CRM-UAM/Vector9000/competiciones/robolid2016/2016-04-08 11.16.23.jpg

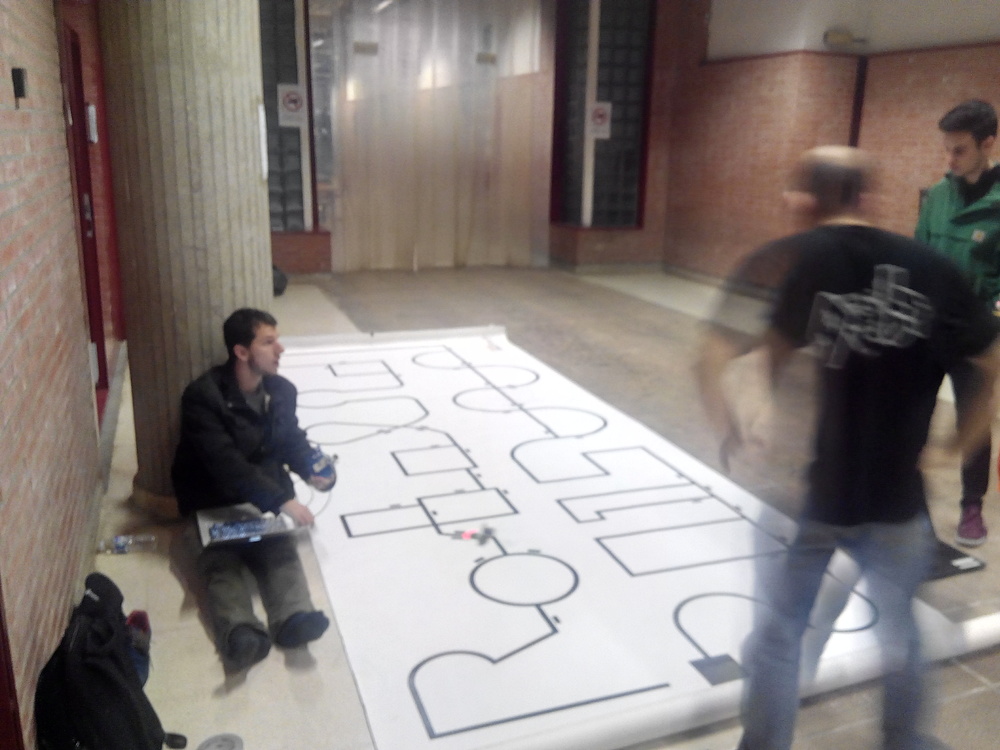
competiciones/robolid2016/2016-04-08 11.16.23.jpg
