CRM-UAM/Vector9000/img/2016-03-30 20.01.13.jpg

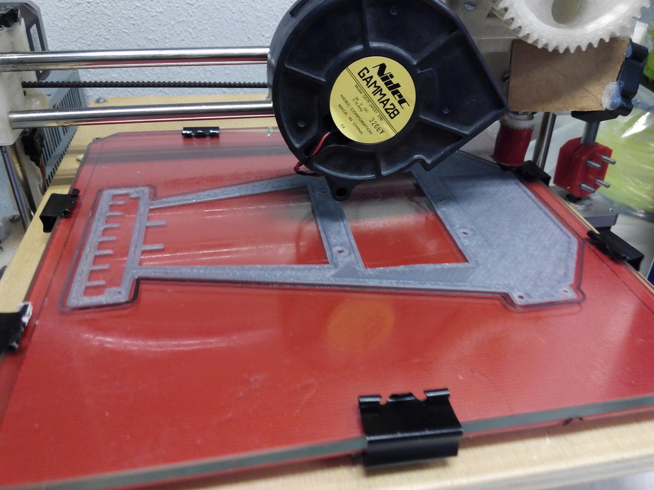
img/2016-03-30 20.01.13.jpg
