CRM-UAM/Vector9000/img/2016-04-03 20.19.17.jpg

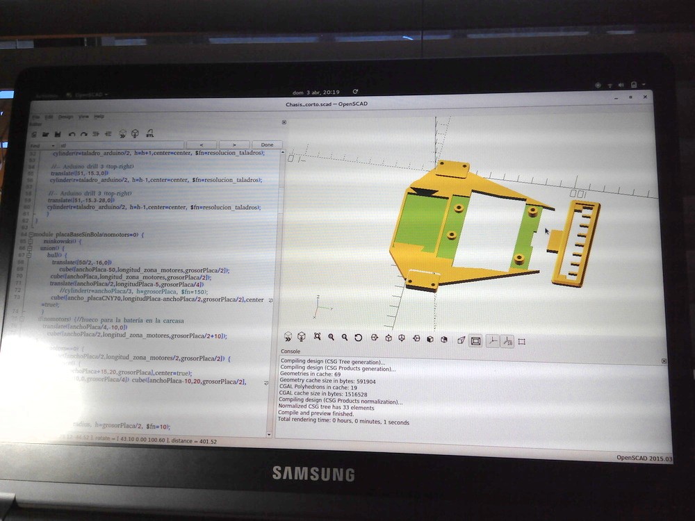
img/2016-04-03 20.19.17.jpg
