CRM-UAM/Vector9000/img/2016-04-04 11.50.08.jpg

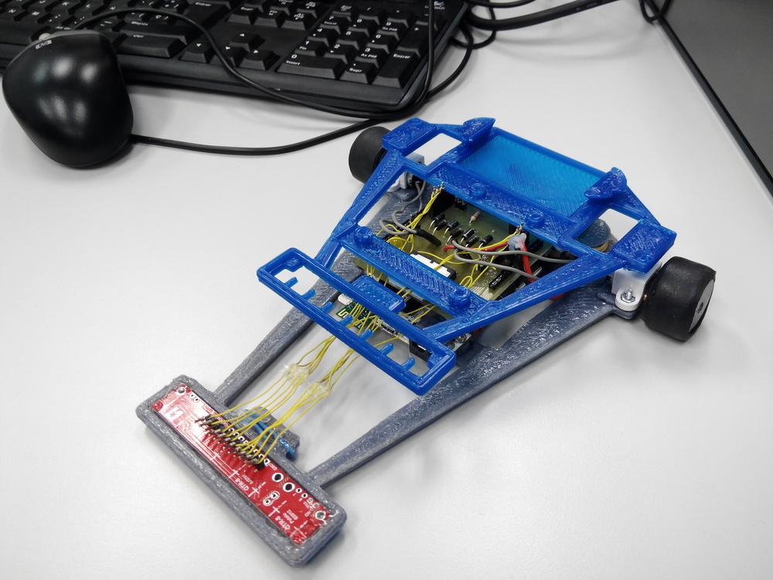
img/2016-04-04 11.50.08.jpg
