CRM-UAM/Vector9000/img/2016-04-08 11.37.30.jpg

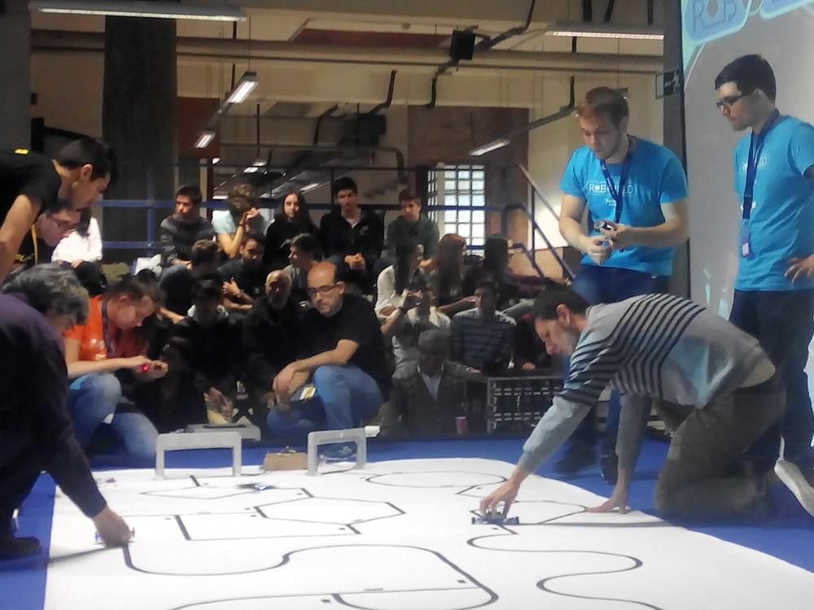
img/2016-04-08 11.37.30.jpg
