CRM-UAM/Vector9000/img/IMG-20160406-WA0005.jpg

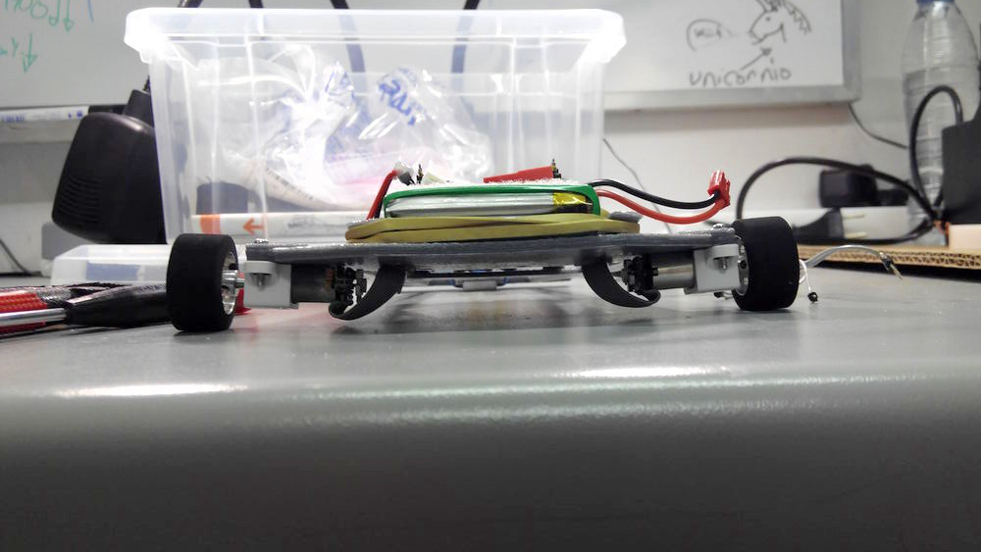
img/IMG-20160406-WA0005.jpg
