CRM-UAM/Vector9000/img/IMG-20160407-WA0009.jpg

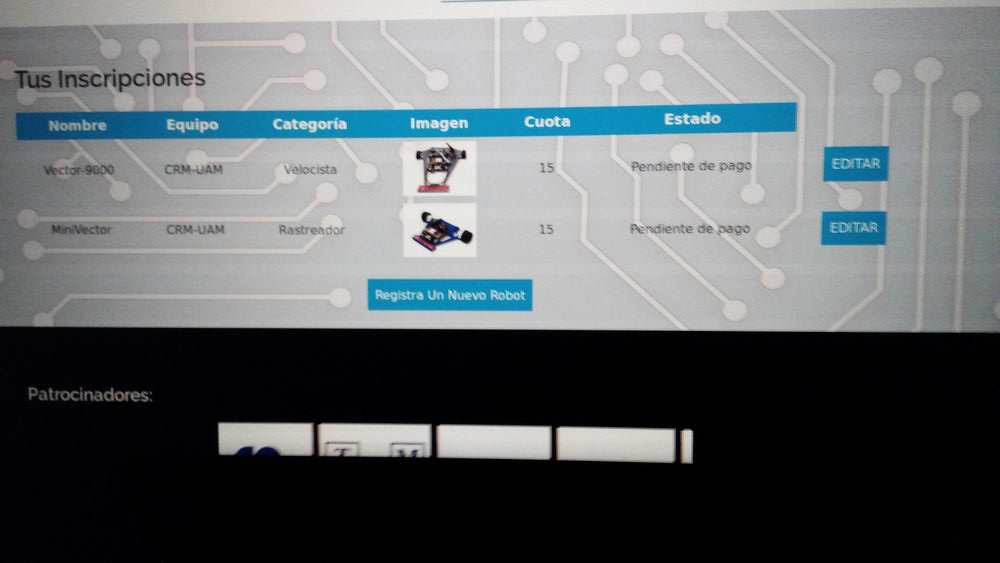
img/IMG-20160407-WA0009.jpg
