CRM-UAM/Vector9000/img/robots_robolid2016.jpg

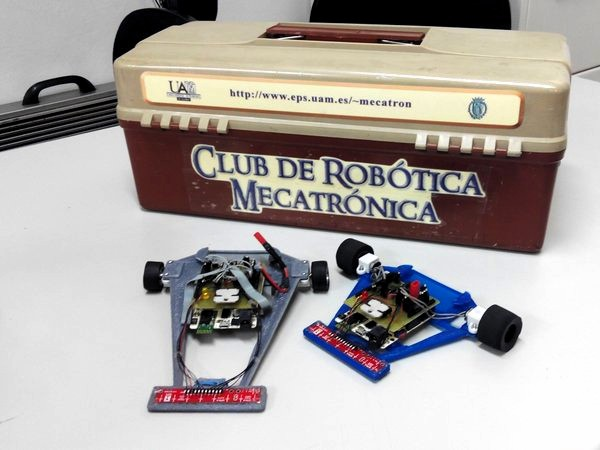
img/robots_robolid2016.jpg
