CRM-UAM/Vector9000/img/vector9000_v3_7apr2016_robolid.jpeg

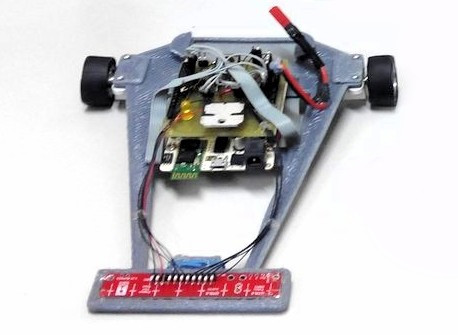
img/vector9000_v3_7apr2016_robolid.jpeg
